Andrew123098/GEEN_2400/CAD/Photos/RightViewNew1.PNG

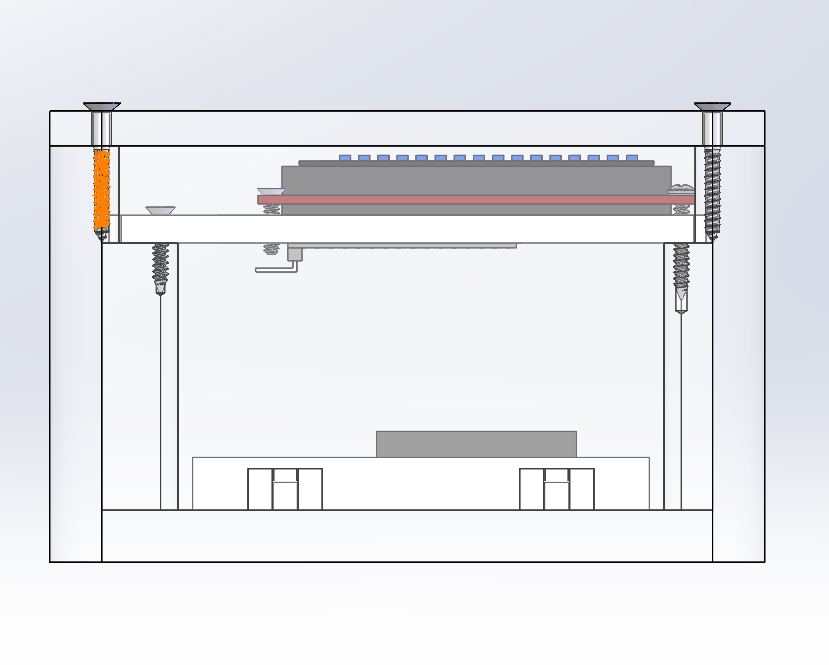
CAD/Photos/RightViewNew1.PNG
