Andrew123098/GEEN_2400/CAD/Photos/U Clamp Mounting Positions.PNG

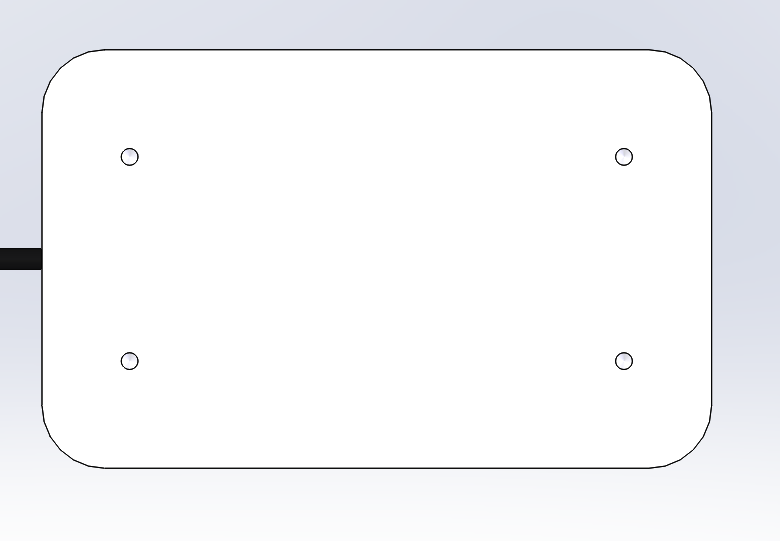
CAD/Photos/U Clamp Mounting Positions.PNG
