Andrew123098/GEEN_2400/Code/temp/src/temp.ino

/*
 * Project temp
 * Description:
 * Author:
 * Date:
 */

// setup() runs once, when the device is first turned on.
void setup() {
  // Put initialization like pinMode and begin functions here.

}

// loop() runs over and over again, as quickly as it can execute.
void loop() {
  // The core of your code will likely live here.

}
